perriestudios/Indoor-Object-Tracking-with-UWB/Exported_Images/001.png

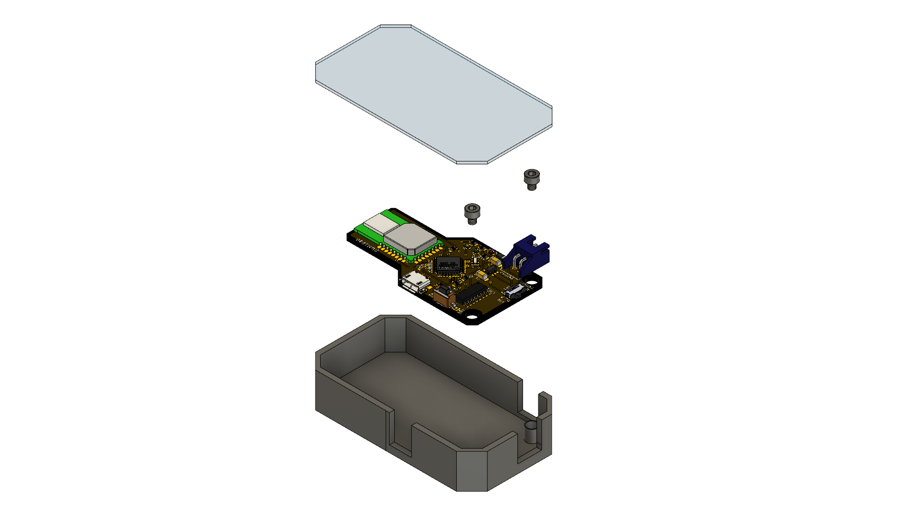
Exported_Images/001.png
