perriestudios/Indoor-Object-Tracking-with-UWB/Exported_Images/002.png

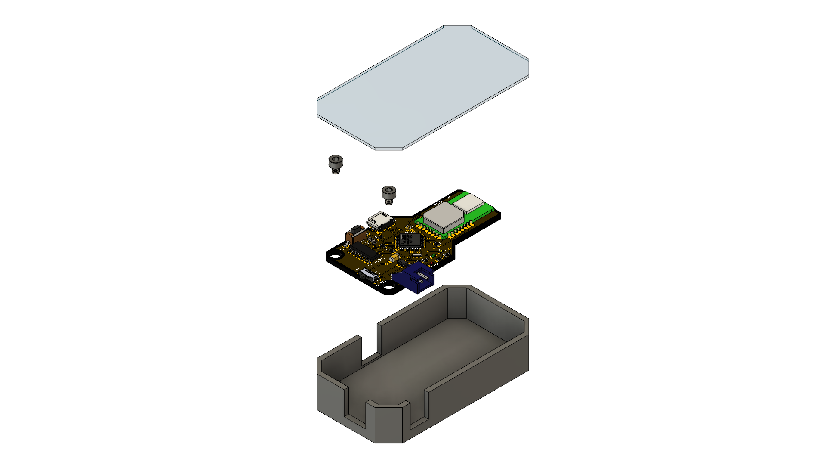
Exported_Images/002.png
