perriestudios/Indoor-Object-Tracking-with-UWB/Exported_Images/005.png

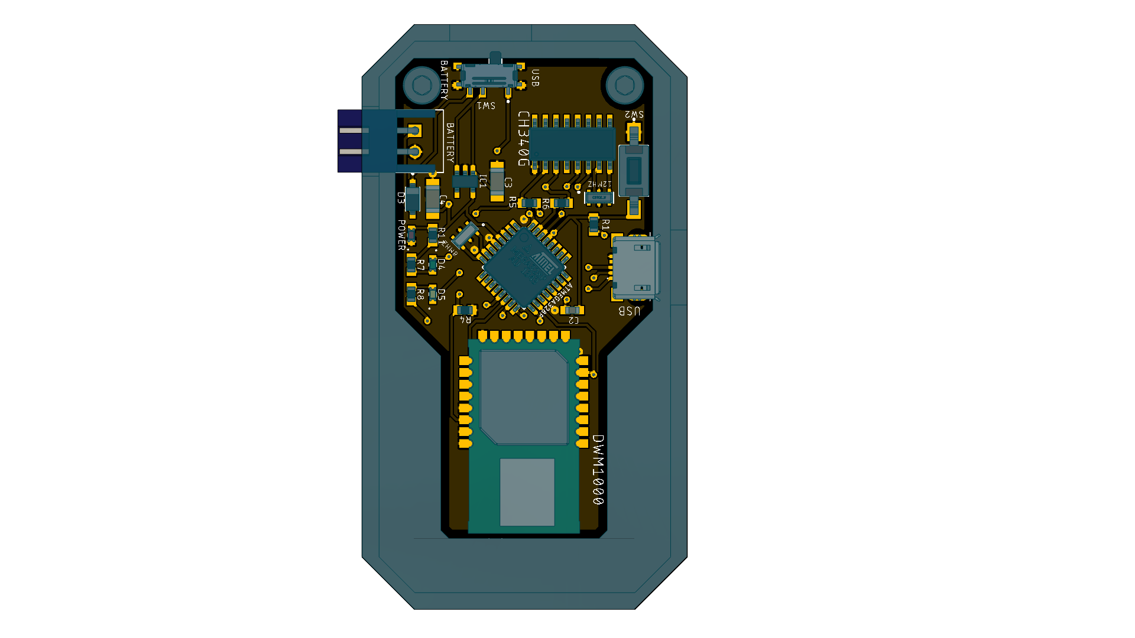
Exported_Images/005.png
