perriestudios/Indoor-Object-Tracking-with-UWB/Exported_Images/006.png

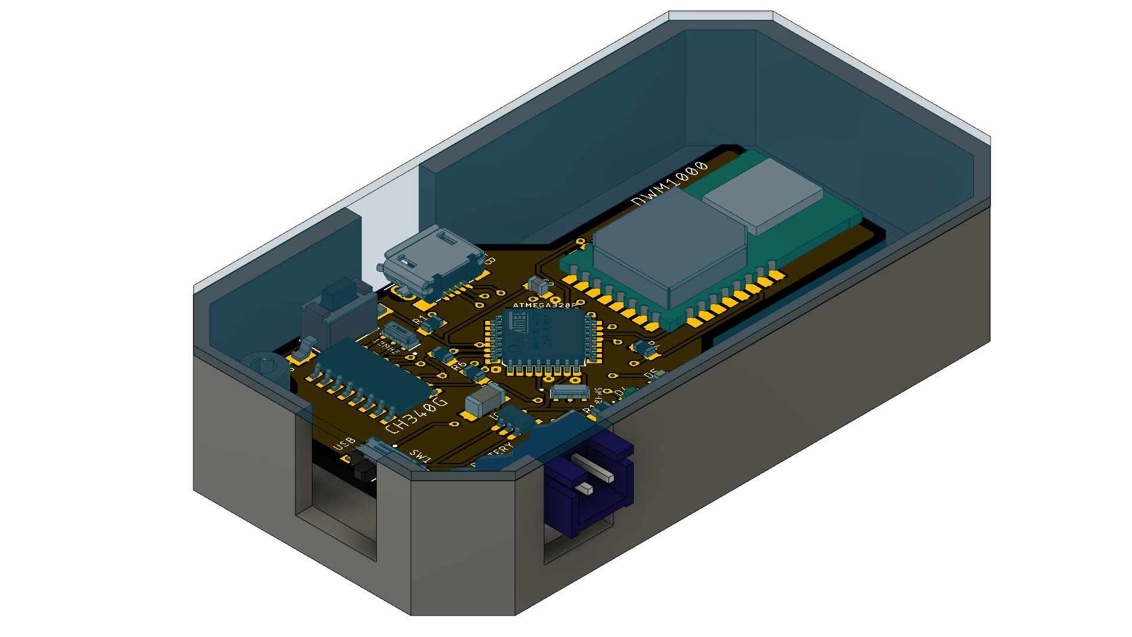
Exported_Images/006.png
