perriestudios/Indoor-Object-Tracking-with-UWB/Exported_Images/007.png

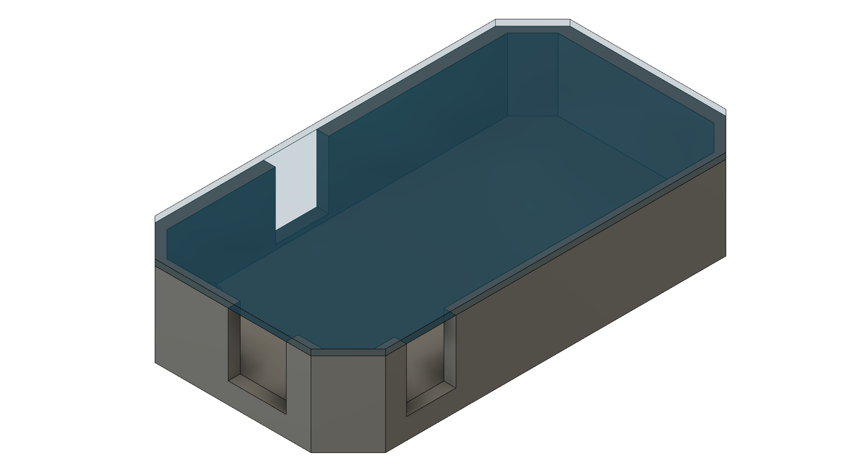
Exported_Images/007.png
