perriestudios/Indoor-Object-Tracking-with-UWB/Exported_Images/008.png

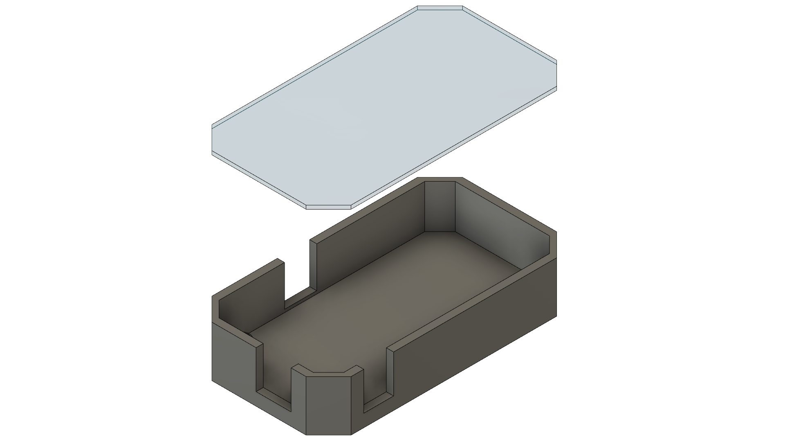
Exported_Images/008.png
