perriestudios/Indoor-Object-Tracking-with-UWB/Exported_Images/image10.png

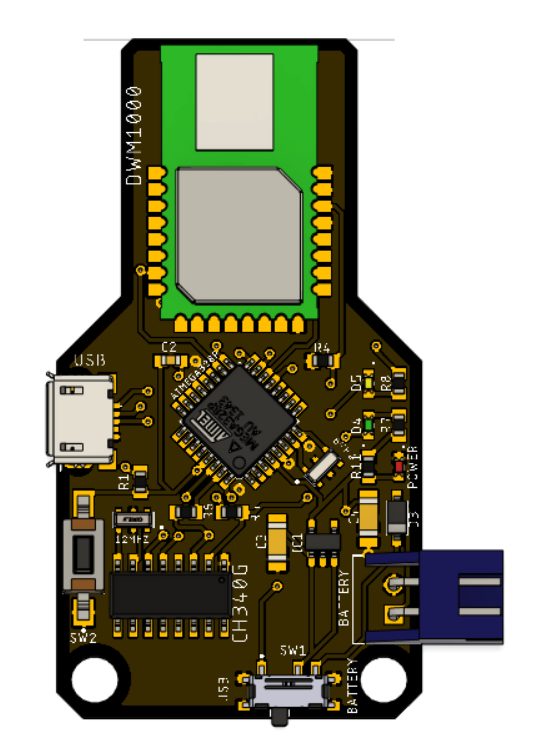
Exported_Images/image10.png
