perriestudios/Indoor-Object-Tracking-with-UWB/Exported_Images/image11.png

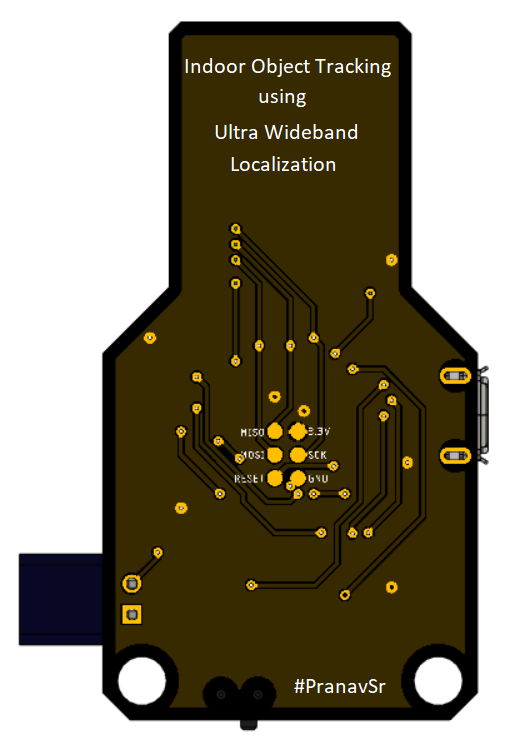
Exported_Images/image11.png
