perriestudios/Indoor-Object-Tracking-with-UWB/Exported_Images/image12.png

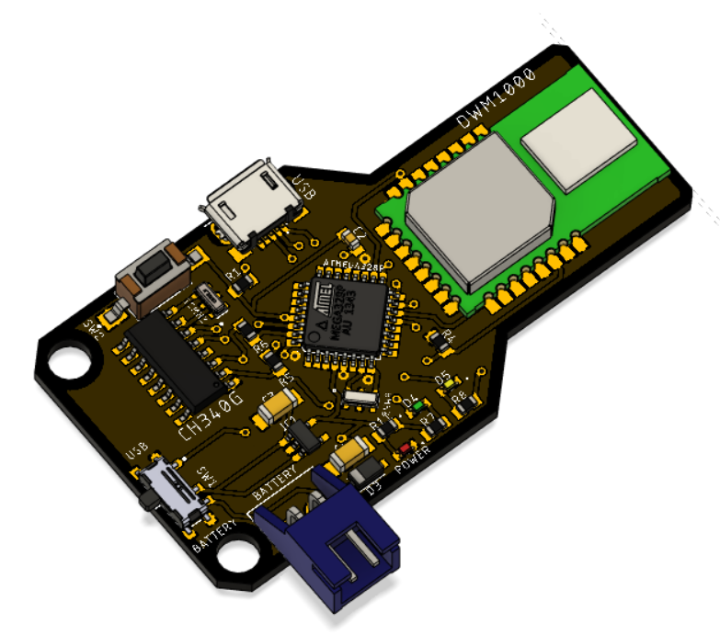
Exported_Images/image12.png
