perriestudios/Indoor-Object-Tracking-with-UWB/Project Pictures/image3.png

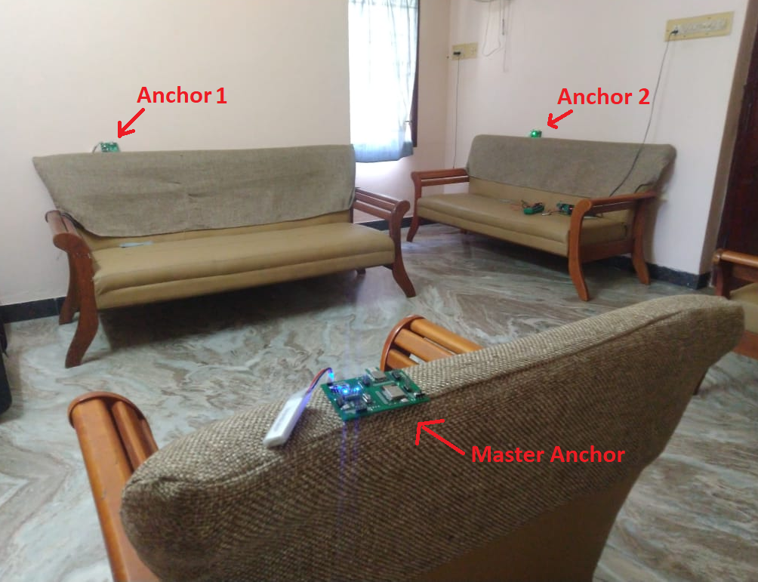
Project Pictures/image3.png
