perriestudios/Indoor-Object-Tracking-with-UWB/Project Pictures/image16.jpeg

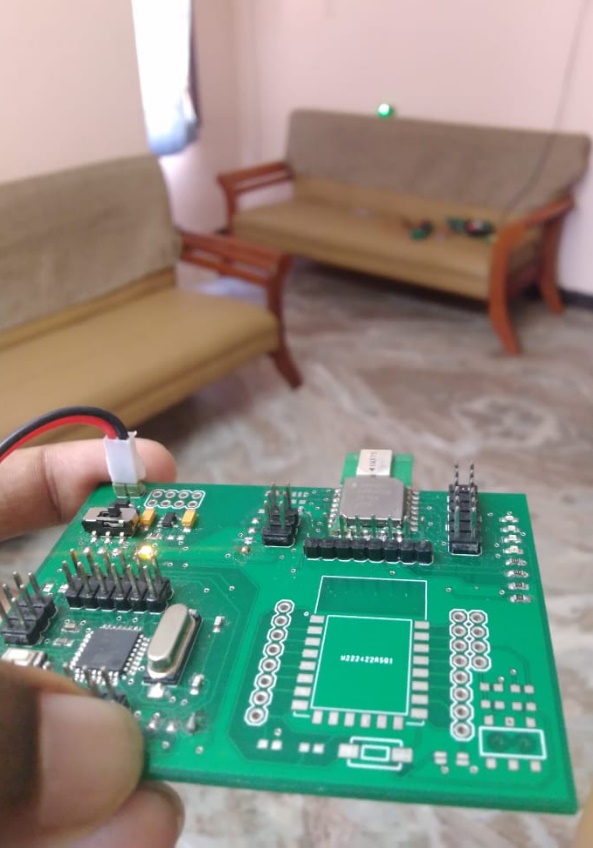
Project Pictures/image16.jpeg
