perriestudios/Indoor-Object-Tracking-with-UWB/Project Pictures/image17.png

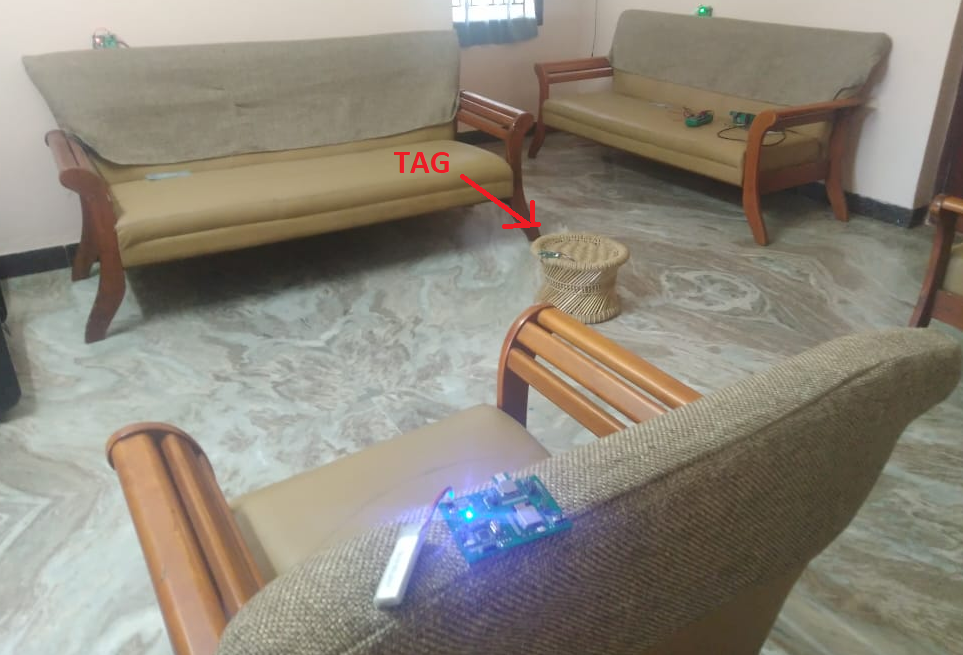
Project Pictures/image17.png
